Carabouille/Alarm_Clock_dawn_simulator/blender/blender_projet/assets/models/lynx-stone-moss-_25901008-8f63-4383-ab6d-80dfdbb805d9/preview.png

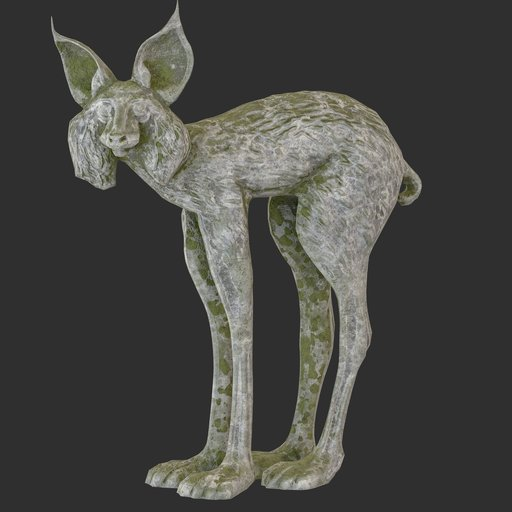
blender/blender_projet/assets/models/lynx-stone-moss-_25901008-8f63-4383-ab6d-80dfdbb805d9/preview.png
