Carabouille/Alarm_Clock_dawn_simulator/blender/blender_projet/assets/models/matcha-fox-rigge_24c6cca8-8f34-4dda-9428-183906118821/preview.png

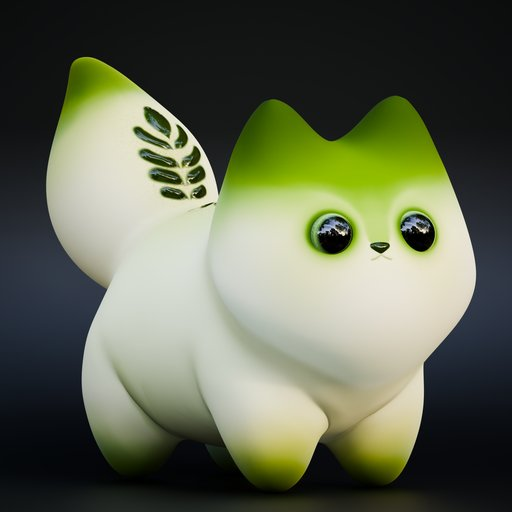
blender/blender_projet/assets/models/matcha-fox-rigge_24c6cca8-8f34-4dda-9428-183906118821/preview.png
