Carabouille/Alarm_Clock_dawn_simulator/blender/blender_projet/assets/models/moss-01_9754e93a-d56c-4a1c-8562-d5b704e4d787/preview.png

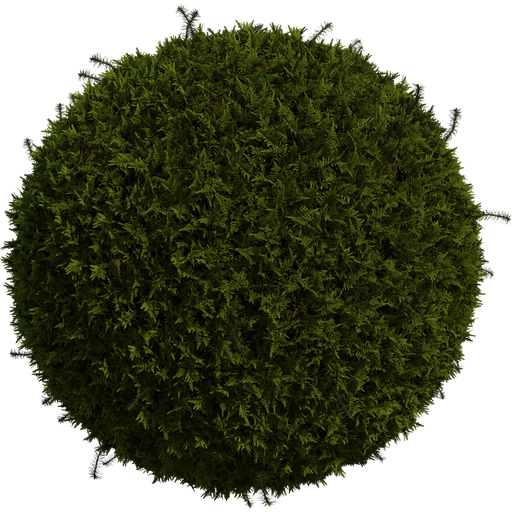
blender/blender_projet/assets/models/moss-01_9754e93a-d56c-4a1c-8562-d5b704e4d787/preview.png
