Carabouille/Alarm_Clock_dawn_simulator/blender/blender_projet/assets/models/wooden-bridge_eeb77a38-bba0-485d-9a47-ced89a95c82b/preview.png

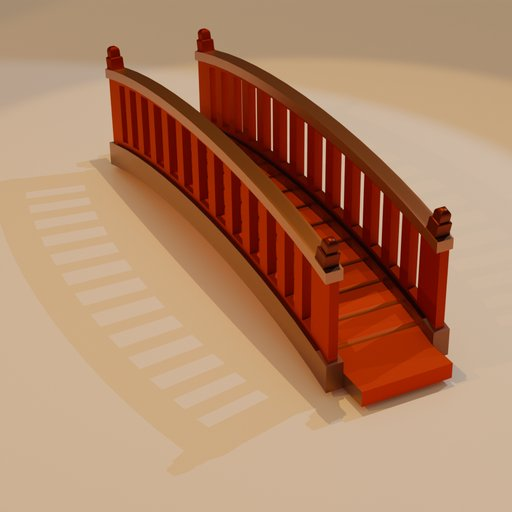
blender/blender_projet/assets/models/wooden-bridge_eeb77a38-bba0-485d-9a47-ced89a95c82b/preview.png
