Carabouille/Alarm_Clock_dawn_simulator/blender/blender_projet/assets/materials/moss_1d86833c-6ca6-4c9e-b02b-61ddcb9549ac/preview.png

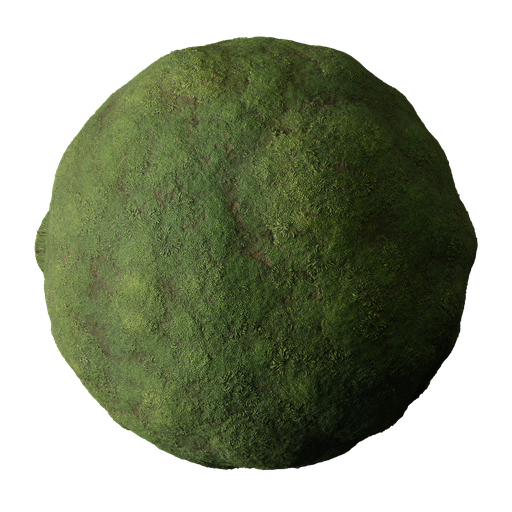
blender/blender_projet/assets/materials/moss_1d86833c-6ca6-4c9e-b02b-61ddcb9549ac/preview.png
