Carabouille/Alarm_Clock_dawn_simulator/blender/blender_projet/assets/materials/tree-bark_1537f13f-c69f-473e-af30-d679511bf8fa/preview.png

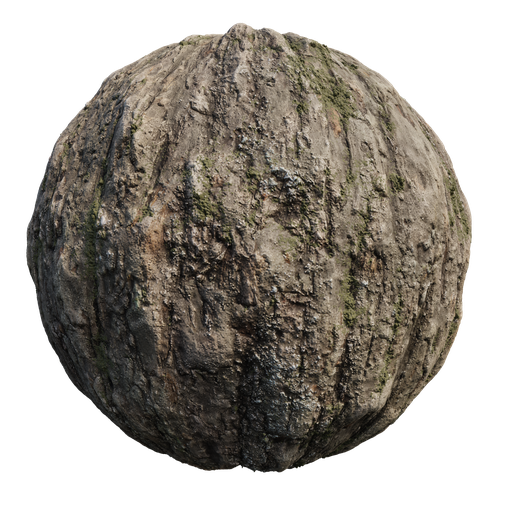
blender/blender_projet/assets/materials/tree-bark_1537f13f-c69f-473e-af30-d679511bf8fa/preview.png
