Carabouille/Alarm_Clock_dawn_simulator/Pictures/BOM3.png

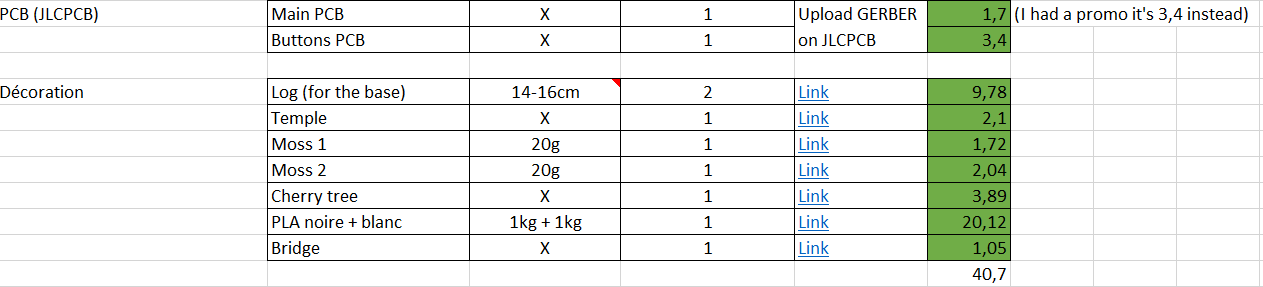
Pictures/BOM3.png
