Carabouille/Alarm_Clock_dawn_simulator/CAD/Solidworks/composant/supp_potar.SLDPRT

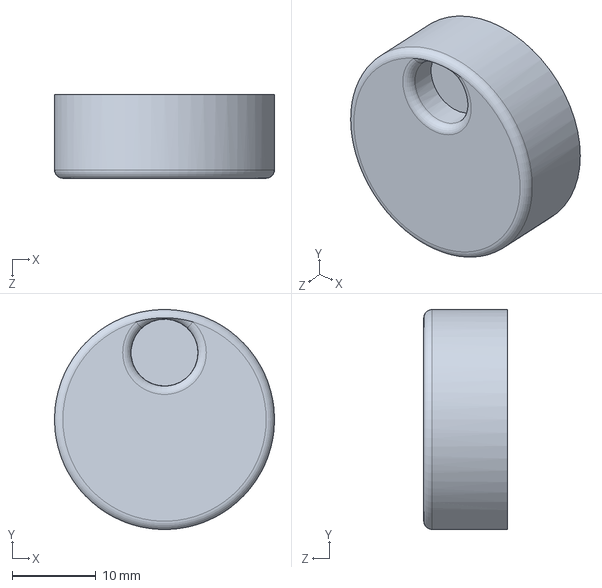
[picture p27: CAD file, 2026-04-21]
CAD/Solidworks/composant/supp_potar.SLDPRT
26.3 x 26.3 x 10.0 mm
