Carabouille/Alarm_Clock_dawn_simulator/CAD/Solidworks/alarm_carte_sd_pcb.SLDPRT

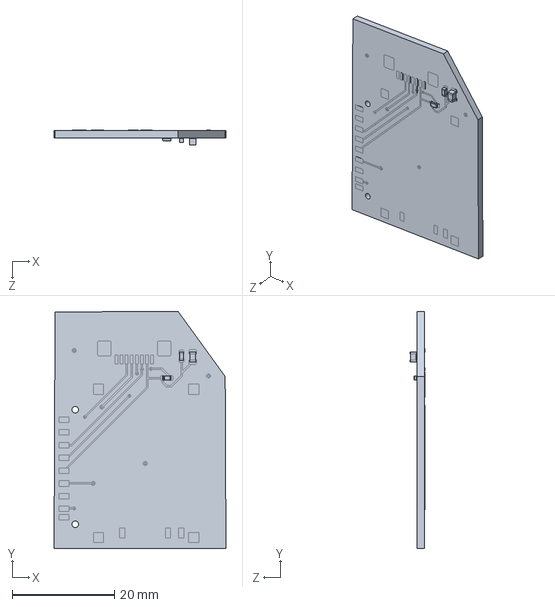
[picture p28: CAD file, 2026-04-21]
CAD/Solidworks/alarm_carte_sd_pcb.SLDPRT
33.6 x 46.4 x 2.88 mm
