Carabouille/Alarm_Clock_dawn_simulator/CAD/Solidworks/composant/supp_dissipateur.SLDPRT

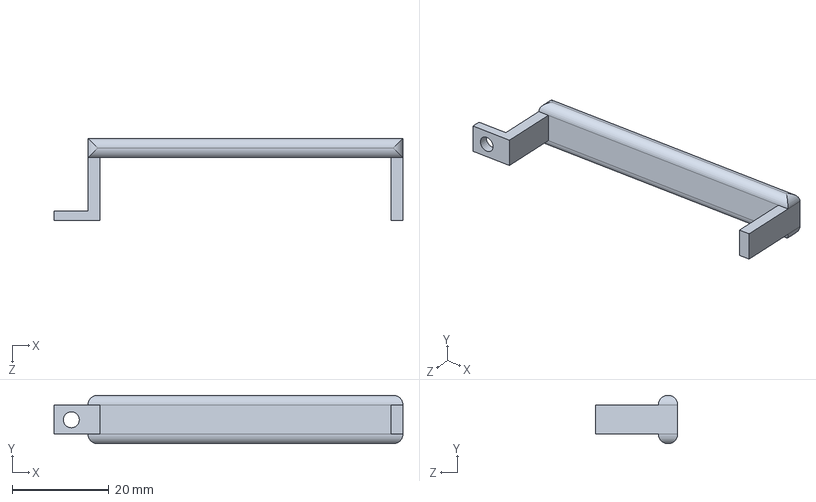
[picture p29: CAD file, 2026-04-21]
CAD/Solidworks/composant/supp_dissipateur.SLDPRT
72.0 x 10.0 x 17.0 mm
