Carabouille/Alarm_Clock_dawn_simulator/STL/tank.STL

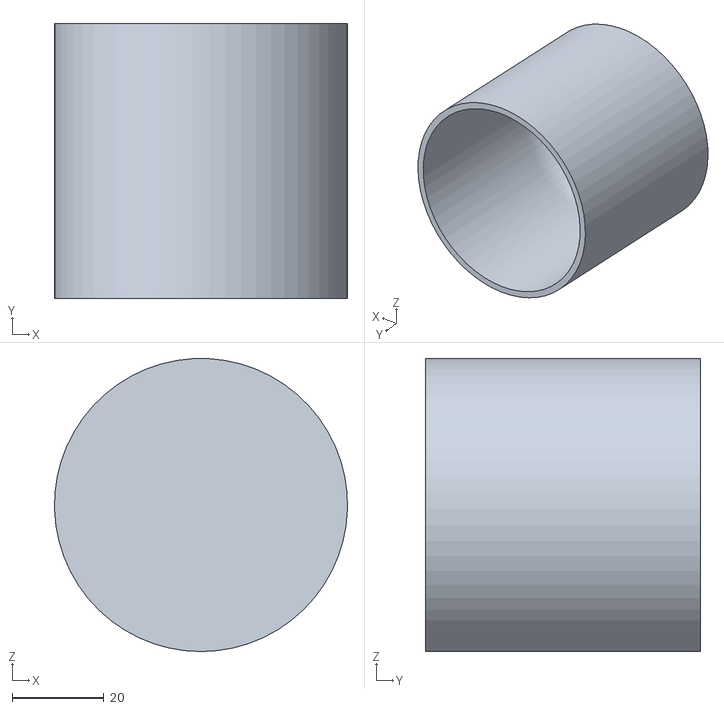
[picture p30: CAD file, 2026-04-21]
STL/tank.STL
64.0 x 60.0 x 64.0
