Carabouille/Alarm_Clock_dawn_simulator/CAD/Solidworks/box_bottom.SLDPRT

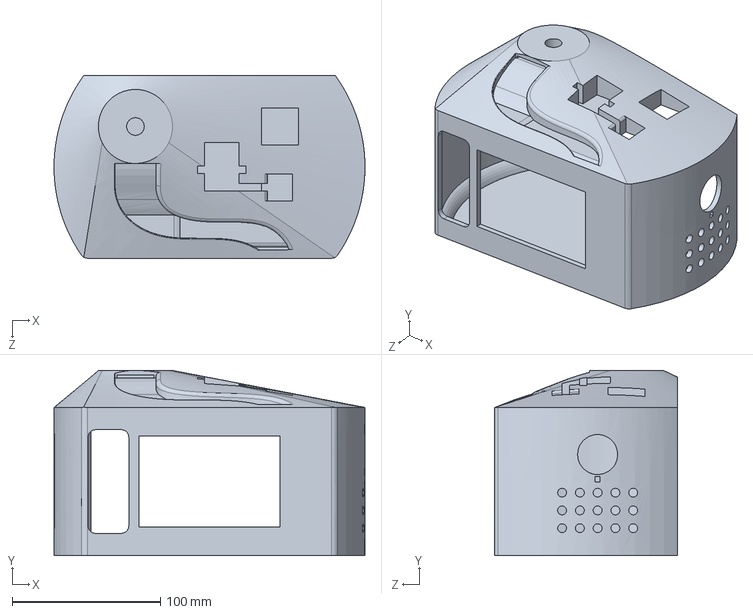
[picture p31: CAD file, 2026-04-21]
CAD/Solidworks/box_bottom.SLDPRT
210.0 x 125.0 x 123.3 mm
