Carabouille/Alarm_Clock_dawn_simulator/CAD/Solidworks/composant/cache_lum.SLDPRT

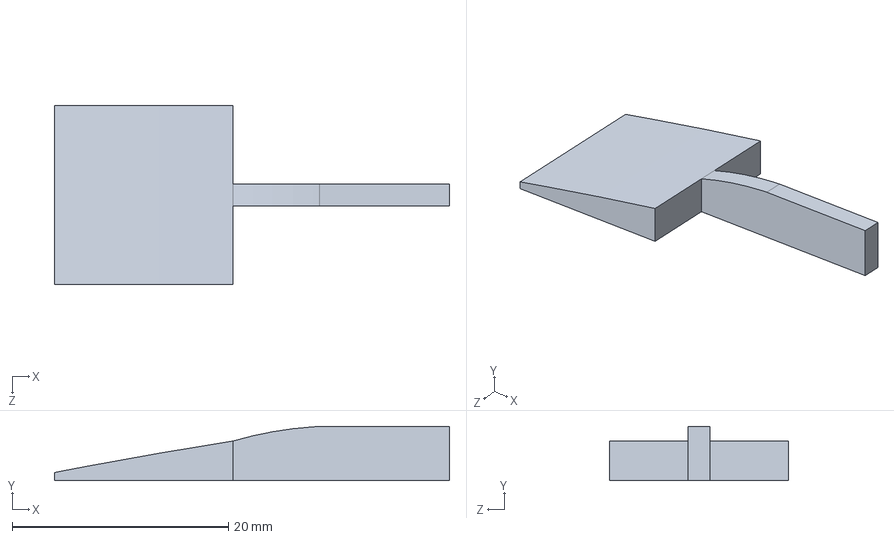
[picture p32: CAD file, 2026-04-21]
CAD/Solidworks/composant/cache_lum.SLDPRT
36.5 x 5.00 x 16.5 mm
