Carabouille/Alarm_Clock_dawn_simulator/STL/tank_cover.STL

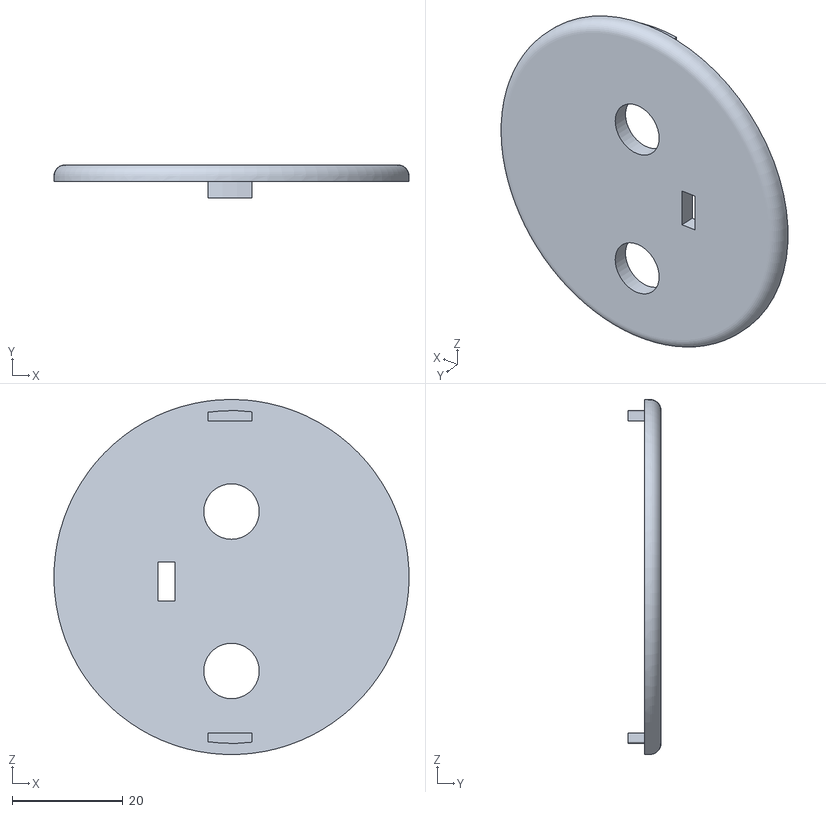
[picture p33: CAD file, 2026-04-21]
STL/tank_cover.STL
64.0 x 6.00 x 64.0
