Carabouille/Alarm_Clock_dawn_simulator/CAD/Solidworks/composant/servo_moteur.SLDPRT

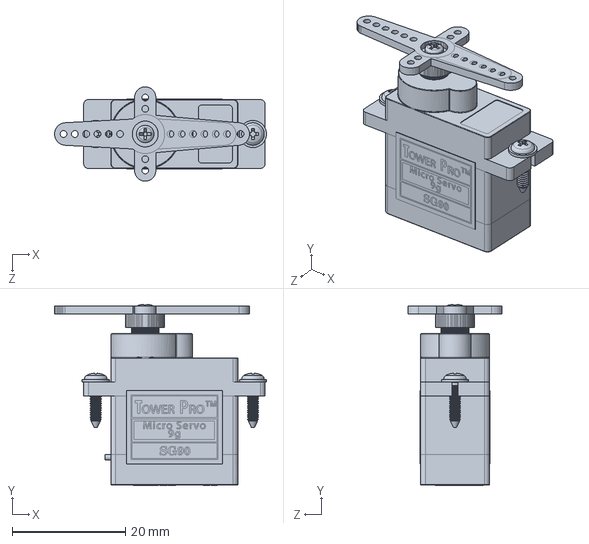
[picture p34: CAD file, 2026-04-21]
CAD/Solidworks/composant/servo_moteur.SLDPRT
37.5 x 32.0 x 16.7 mm
