Carabouille/Alarm_Clock_dawn_simulator/CAD/Solidworks/extension_btn_vfinal_UwU.SLDPRT

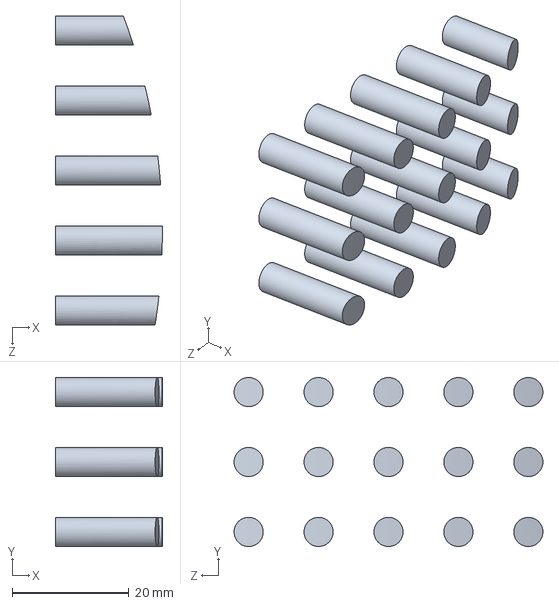
[picture p35: CAD file, 2026-04-21]
CAD/Solidworks/extension_btn_vfinal_UwU.SLDPRT
18.3 x 29.0 x 53.0 mm
