Carabouille/Alarm_Clock_dawn_simulator/CAD/Solidworks/composant/dissipateur.SLDPRT

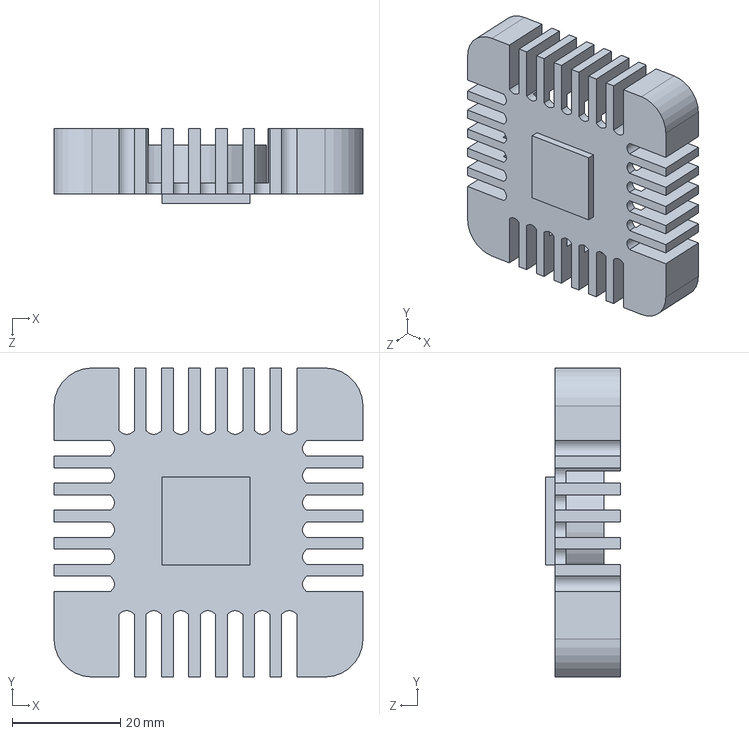
[picture p36: CAD file, 2026-04-21]
CAD/Solidworks/composant/dissipateur.SLDPRT
57.0 x 57.0 x 13.8 mm
