Carabouille/Alarm_Clock_dawn_simulator/CAD/Solidworks/uwuface.SLDPRT

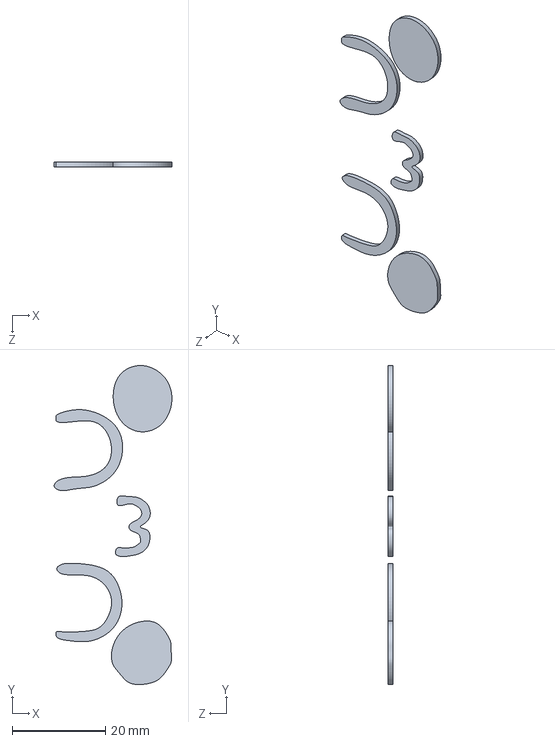
[picture p37: CAD file, 2026-04-21]
CAD/Solidworks/uwuface.SLDPRT
25.3 x 68.4 x 1.00 mm
