Carabouille/Alarm_Clock_dawn_simulator/CAD/Solidworks/composant/screen.SLDPRT

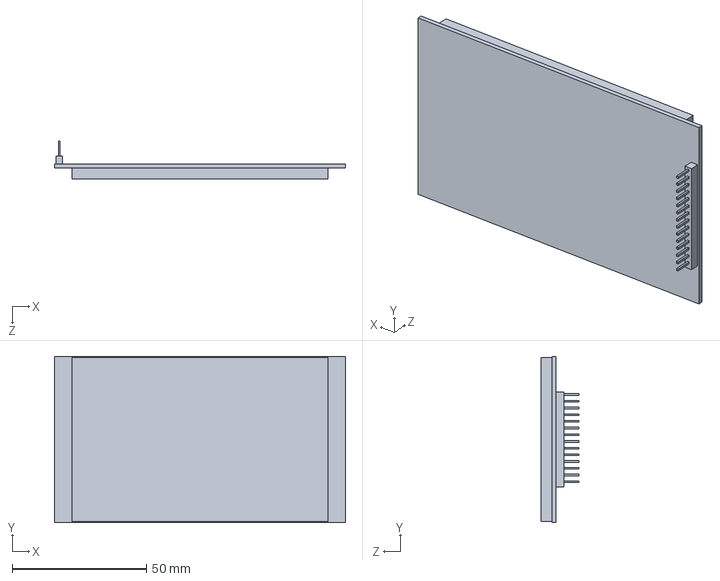
[picture p38: CAD file, 2026-04-21]
CAD/Solidworks/composant/screen.SLDPRT
108.5 x 62.0 x 14.0 mm
