Carabouille/Alarm_Clock_dawn_simulator/CAD/Solidworks/supp_pcb_btn.SLDPRT

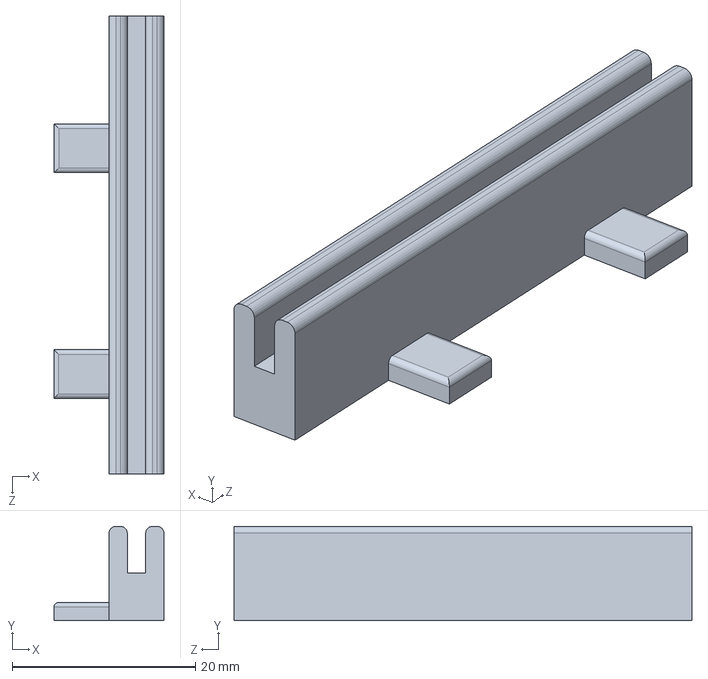
[picture p39: CAD file, 2026-04-21]
CAD/Solidworks/supp_pcb_btn.SLDPRT
12.0 x 10.3 x 50.0 mm
