Carabouille/Alarm_Clock_dawn_simulator/CAD/Solidworks/box_top.SLDPRT

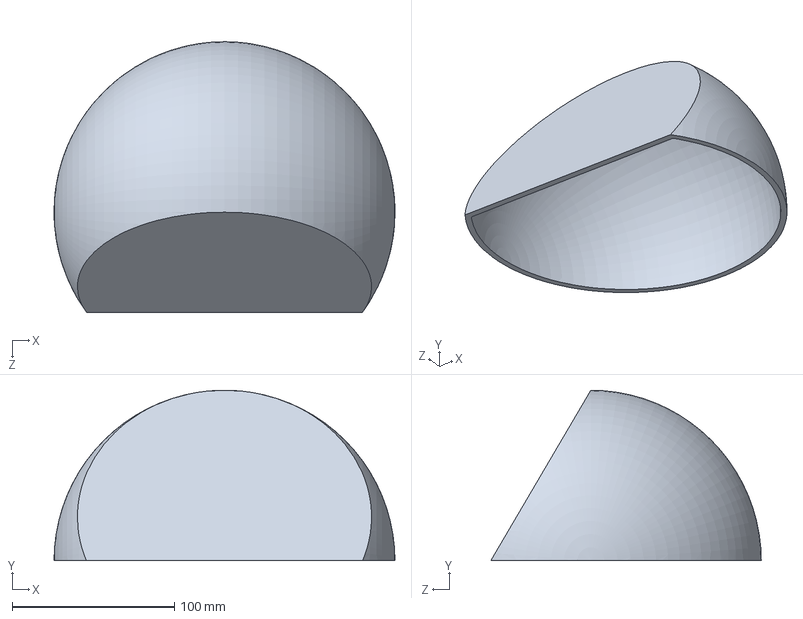
[picture p40: CAD file, 2026-04-21]
CAD/Solidworks/box_top.SLDPRT
210.0 x 105.0 x 166.6 mm
