Carabouille/Alarm_Clock_dawn_simulator/CAD/Solidworks/composant/couvercle_recipient.SLDPRT

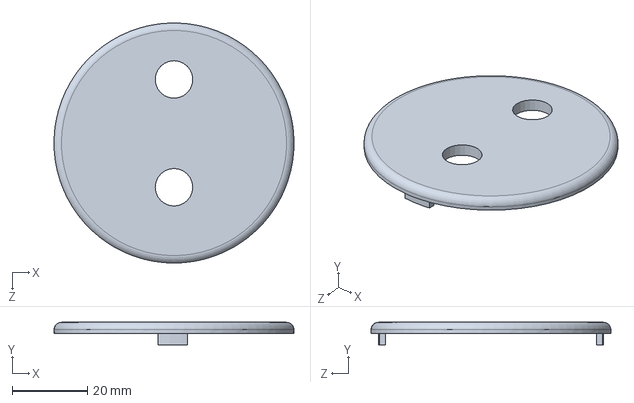
[picture p41: CAD file, 2026-04-21]
CAD/Solidworks/composant/couvercle_recipient.SLDPRT
64.0 x 6.00 x 64.0 mm
