Carabouille/Alarm_Clock_dawn_simulator/CAD/Solidworks/composant/hp.SLDPRT

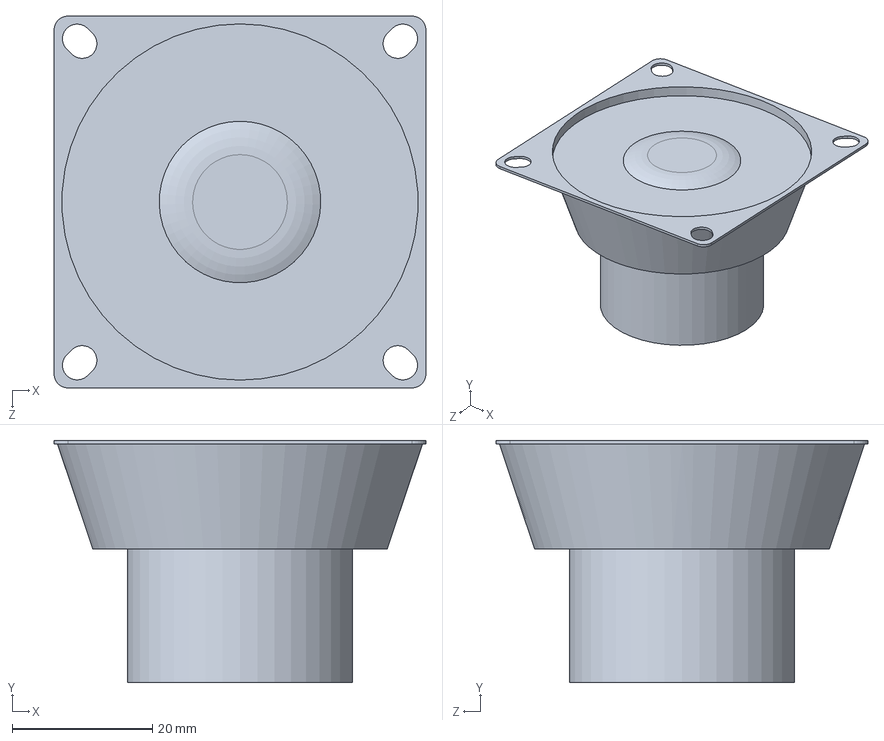
[picture p42: CAD file, 2026-04-21]
CAD/Solidworks/composant/hp.SLDPRT
53.0 x 34.5 x 53.0 mm
