Carabouille/Alarm_Clock_dawn_simulator/CAD/Solidworks/composant/USB_C_port.SLDPRT

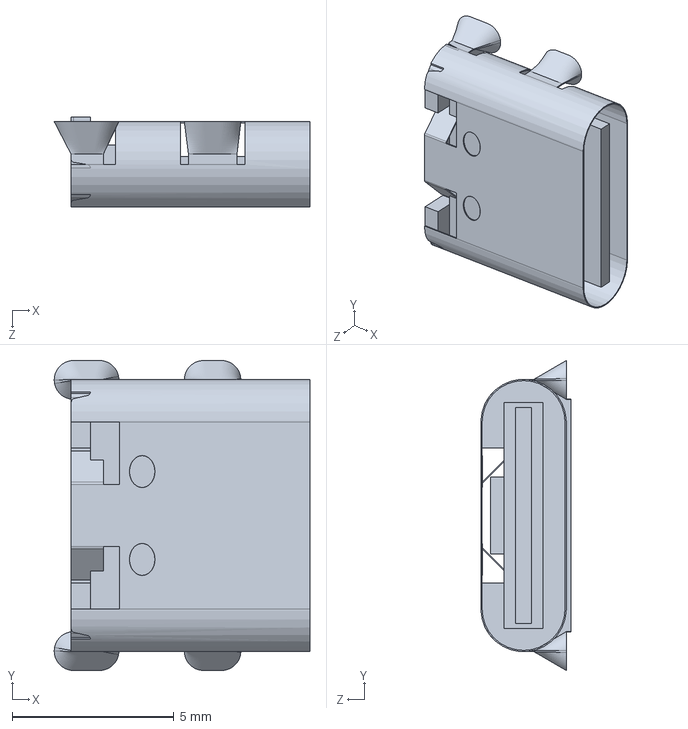
[picture p43: CAD file, 2026-04-21]
CAD/Solidworks/composant/USB_C_port.SLDPRT
7.90 x 9.58 x 2.79 mm
