Carabouille/Alarm_Clock_dawn_simulator/CAD/Solidworks/supp_carte_sd.SLDPRT

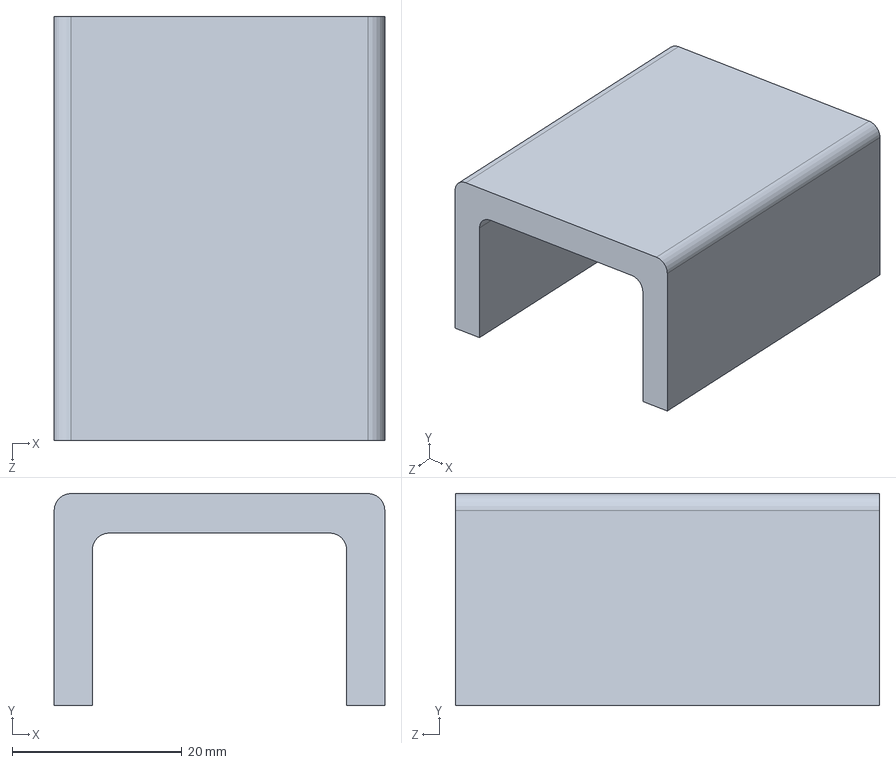
[picture p44: CAD file, 2026-04-21]
CAD/Solidworks/supp_carte_sd.SLDPRT
39.0 x 25.0 x 50.0 mm
