Carabouille/Alarm_Clock_dawn_simulator/CAD/Solidworks/composant/batterie 18650.SLDPRT

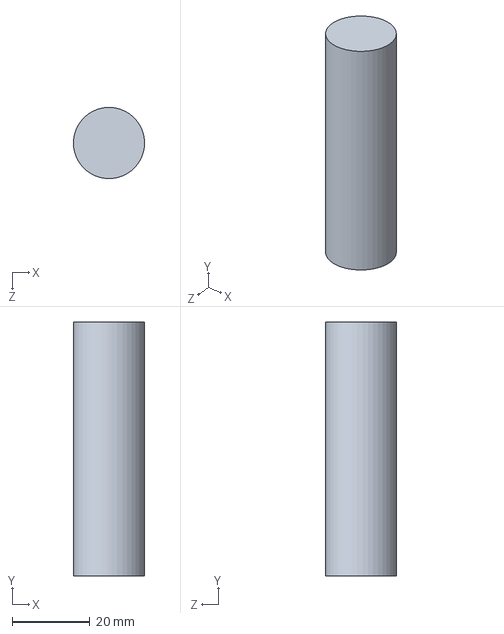
[picture p45: CAD file, 2026-04-21]
CAD/Solidworks/composant/batterie 18650.SLDPRT
18.3 x 65.2 x 18.3 mm
