Carabouille/Alarm_Clock_dawn_simulator/CAD/Solidworks/supp_usbc_port.SLDPRT

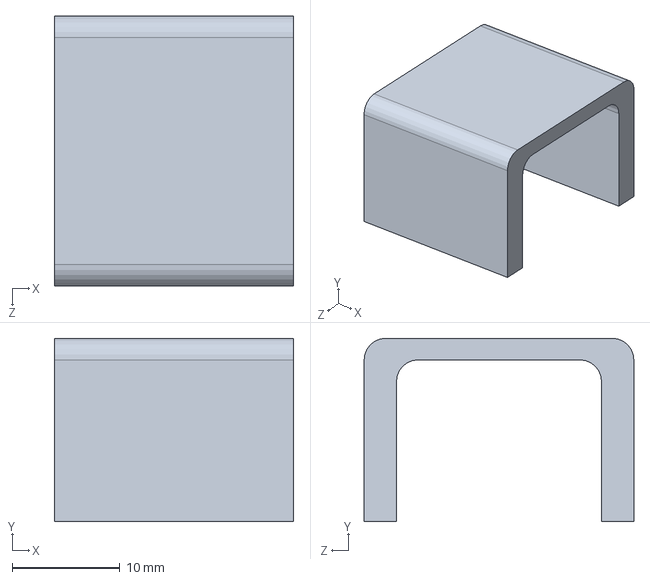
[picture p46: CAD file, 2026-04-21]
CAD/Solidworks/supp_usbc_port.SLDPRT
22.1 x 17.0 x 25.0 mm
