Carabouille/Alarm_Clock_dawn_simulator/CAD/Solidworks/supp_pcb_btnVpinhaut.SLDPRT

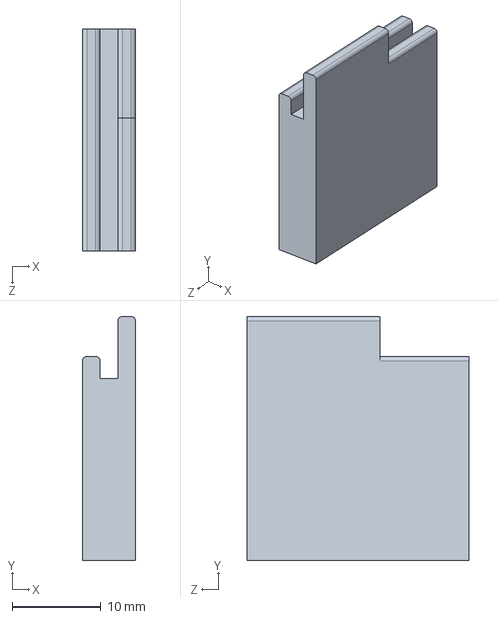
[picture p47: CAD file, 2026-04-21]
CAD/Solidworks/supp_pcb_btnVpinhaut.SLDPRT
6.00 x 27.5 x 25.0 mm
