Carabouille/Alarm_Clock_dawn_simulator/CAD/Solidworks/back_box.SLDPRT

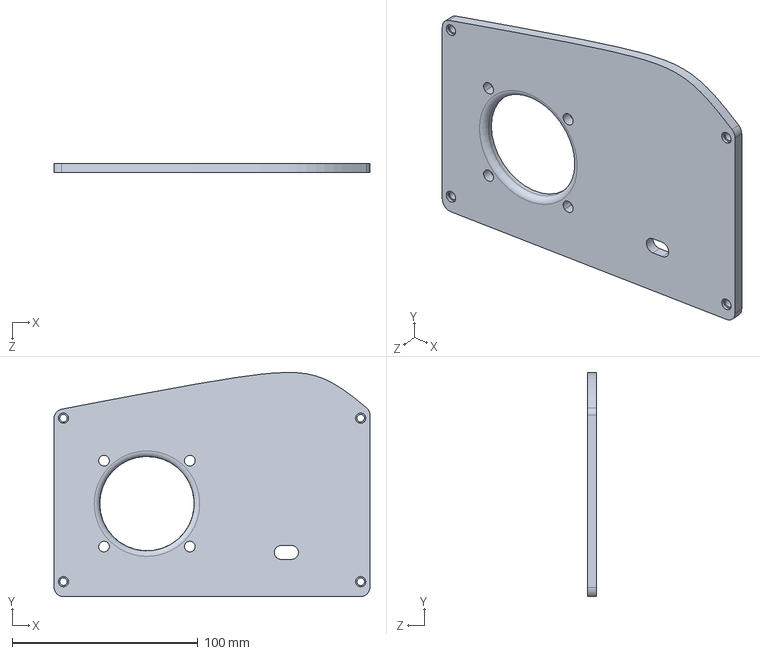
[picture p48: CAD file, 2026-04-21]
CAD/Solidworks/back_box.SLDPRT
170.0 x 120.6 x 5.00 mm
