Carabouille/Alarm_Clock_dawn_simulator/CAD/Solidworks/recup_riviere.SLDPRT

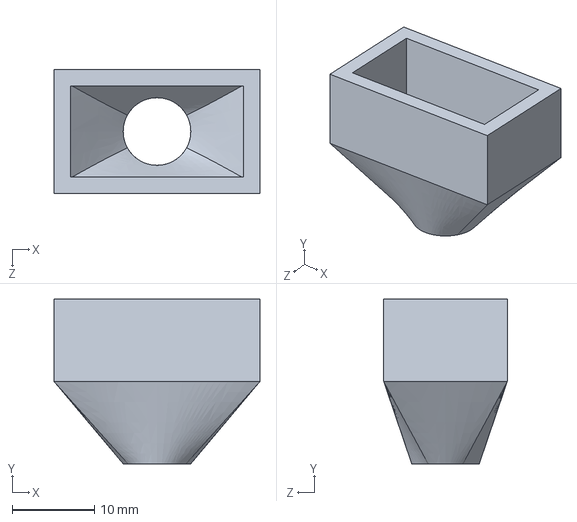
[picture p49: CAD file, 2026-04-21]
CAD/Solidworks/recup_riviere.SLDPRT
25.0 x 20.0 x 15.0 mm
