Carabouille/Alarm_Clock_dawn_simulator/CAD/Solidworks/supp_switch.SLDPRT

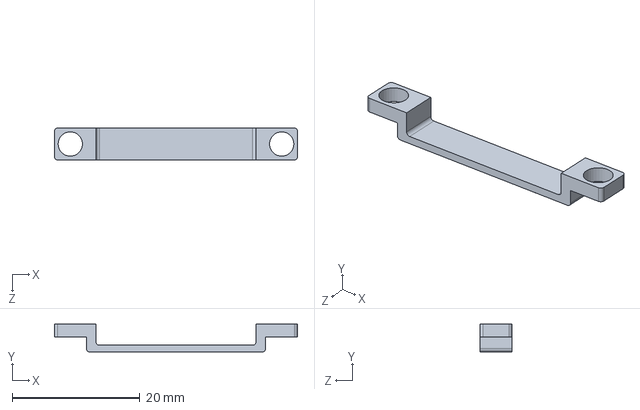
[picture p50: CAD file, 2026-04-21]
CAD/Solidworks/supp_switch.SLDPRT
38.0 x 4.36 x 5.00 mm
