Carabouille/Alarm_Clock_dawn_simulator/CAD/Solidworks/socle bois.SLDPRT

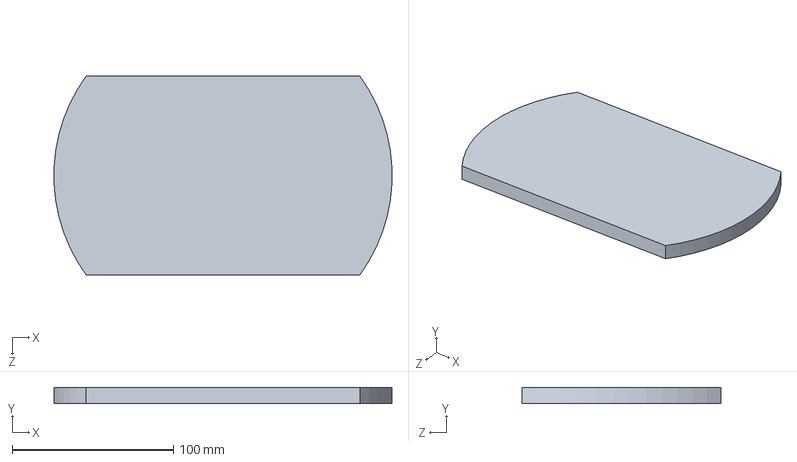
[picture p51: CAD file, 2026-04-21]
CAD/Solidworks/socle bois.SLDPRT
209.8 x 10.0 x 123.3 mm
